tim-in-oakton/ESP8266Kegerator/Docs and Pics/tap handle -3d printed.jpg

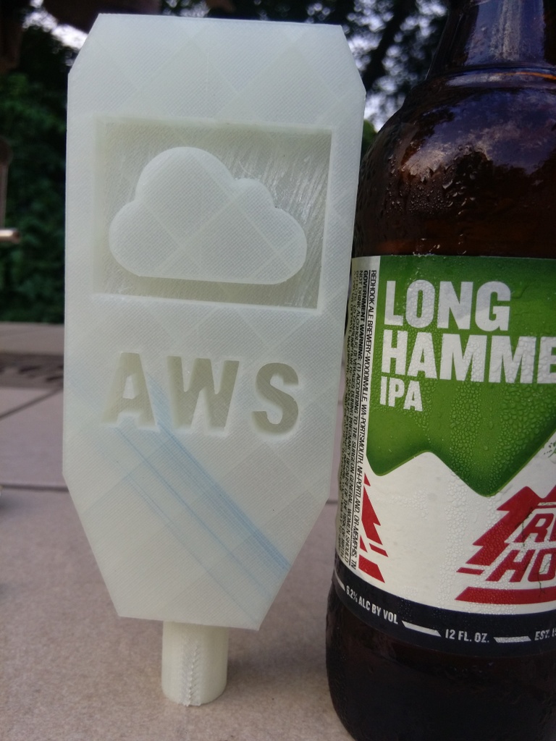
Docs and Pics/tap handle -3d printed.jpg
