tim-in-oakton/ESP8266Kegerator/Kegerator-v5.6_hysteresis-fixed.ino/sha256.h

/*

Using HMAC-SHA-256:
  #include "sha256.h"
  ...
  uint8_t *hash;
  Sha256.initHmac("hash key",8); // key, and length of key in bytes
  Sha256.print("This is a message to hash");
  hash = Sha256.resultHmac();

  The hash result is then stored in hash[0], hash[1] .. hash[31].
*/

#ifndef Sha256_h
#define Sha256_h

#include <inttypes.h>
#include "Print.h"

#define HASH_LENGTH 32
#define BLOCK_LENGTH 64

union _buffer {
  uint8_t b[BLOCK_LENGTH];
  uint32_t w[BLOCK_LENGTH / 4];
};
union _state {
  uint8_t b[HASH_LENGTH];
  uint32_t w[HASH_LENGTH / 4];
};

class Sha256Class : public Print
{
  public:
    void init(void);
    void initHmac(const uint8_t* secret, int secretLength);
    uint8_t* result(void);
    uint8_t* resultHmac(void);
    virtual size_t write(uint8_t);
    using Print::write;
  private:
    void pad();
    void addUncounted(uint8_t data);
    void hashBlock();
    uint32_t ror32(uint32_t number, uint8_t bits);
    _buffer buffer;
    uint8_t bufferOffset;
    _state state;
    uint32_t byteCount;
    uint8_t keyBuffer[BLOCK_LENGTH];
    uint8_t innerHash[HASH_LENGTH];
};
extern Sha256Class Sha256;

#endif
